washishi/NanoMIC/docs/images/IMG20250601211806.jpg

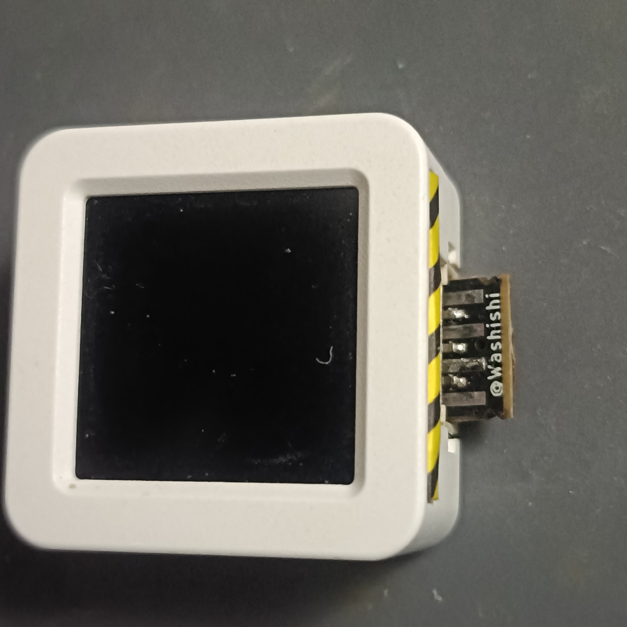
docs/images/IMG20250601211806.jpg
